red5alex/hall-effect-gas-meter-sensor/arduino-sketch/are_wifi.h

#include <WiFi.h>

void connect_to_wifi(const char* ssid, const char* password, const char* hostname ) {
  Serial.print("Connecting to WiFi...");
  WiFi.disconnect(true);
  WiFi.config(INADDR_NONE, INADDR_NONE, INADDR_NONE);
  WiFi.begin(ssid, password);
  WiFi.setHostname(hostname);
  while (WiFi.status() != WL_CONNECTED) { // Flash LED while connecting to WiFi
    for (int i = 0; i <= 5; i++) {
      digitalWrite(GPIO_LED, HIGH);
      delay(50);
      digitalWrite(GPIO_LED, LOW);
      delay(50);
    }
    Serial.print(".");
  }
  Serial.println("WiFi connected.");
  Serial.println(WiFi.localIP());
  digitalWrite(GPIO_LED, HIGH);
  delay(2000);
  digitalWrite(GPIO_LED, LOW);
}
