red5alex/hall-effect-gas-meter-sensor/arduino-sketch/are_wifi_config.h

//#define WIFI_SSID --> Create this in credentials.h
//#define WIFI_PASSWORD --> Create this in credentials.h
#define WIFI_HOSTNAME "esp32-gasmeter"

#define GPIO_LED 2  // the GPIO the LED is connected to (on ESP32-DEVKIT 1 this is GPIO 2)
