red5alex/hall-effect-gas-meter-sensor/arduino-sketch/credentials-template.h

/*  
 * - Make a copy of this file and rename it to 'credentials.h'.
 * - fill in the required credentials for WiFi MQTT broker access.
  */

#define WIFI_SSID "******"
#define WIFI_PASSWORD "*******"
#define MQTT_USER NULL 
#define MQTT_PASSWORD NULL
